Trigger-4622/automotive-telemetry/screens/screen1-round/enclosure/preview/stand.png

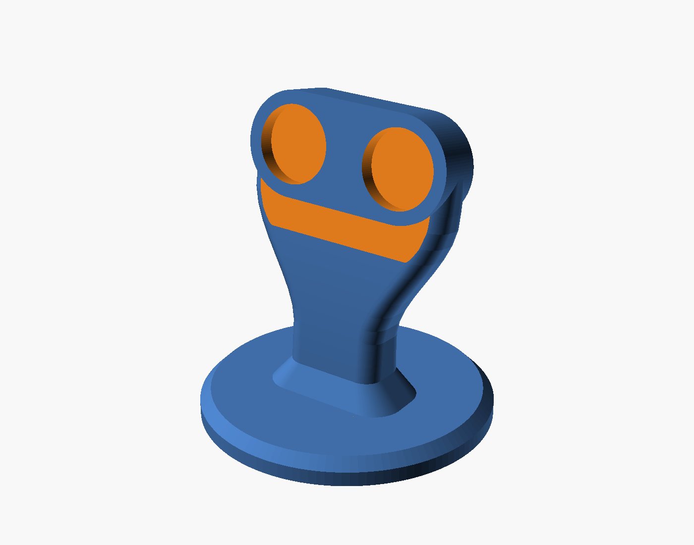
screens/screen1-round/enclosure/preview/stand.png
