Trigger-4622/automotive-telemetry/screens/screen1-round/enclosure/preview/assembly.png

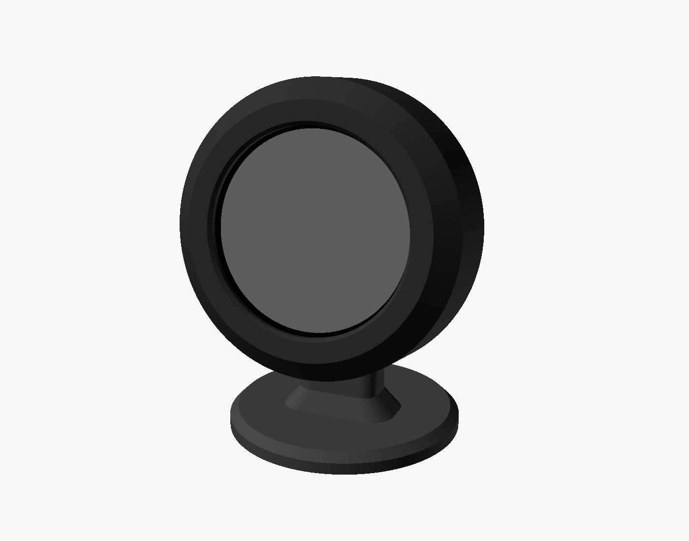
screens/screen1-round/enclosure/preview/assembly.png
