Trigger-4622/automotive-telemetry/screens/screen1-round/enclosure/preview/assembly_back.png

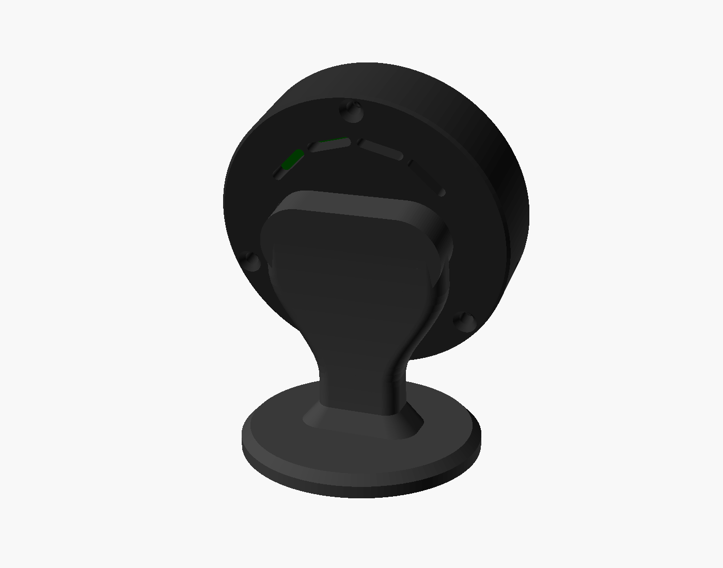
screens/screen1-round/enclosure/preview/assembly_back.png
