Trigger-4622/automotive-telemetry/screens/screen1-round/enclosure/preview/assembly_low.png

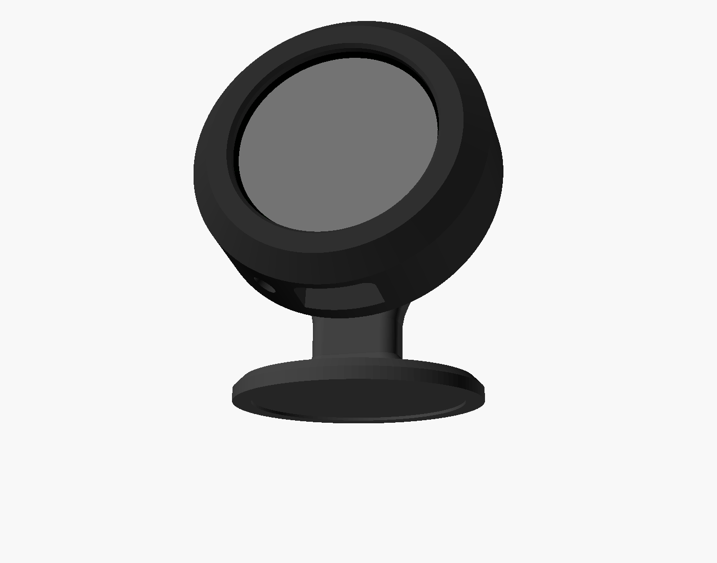
screens/screen1-round/enclosure/preview/assembly_low.png
