Trigger-4622/automotive-telemetry/screens/screen1-round/enclosure/preview/assembly_side.png

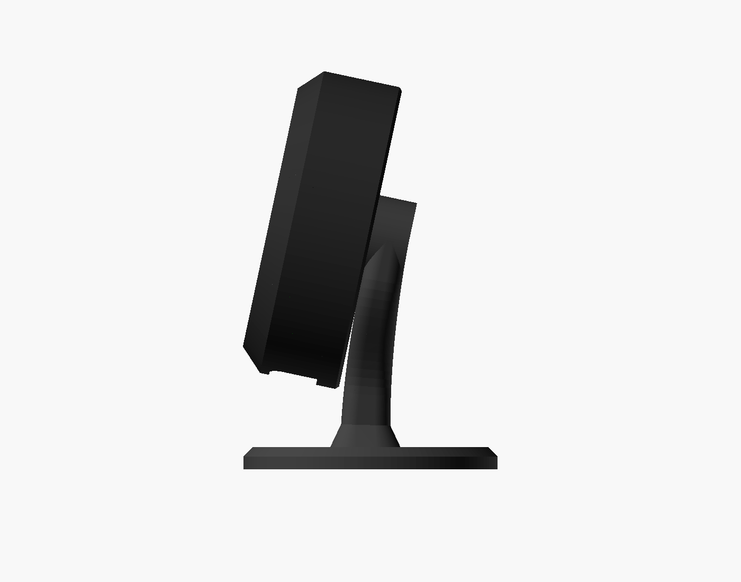
screens/screen1-round/enclosure/preview/assembly_side.png
